jakunzler/bancada-didatica/imagens/800px-Microrregiao_do_Moxoto.png

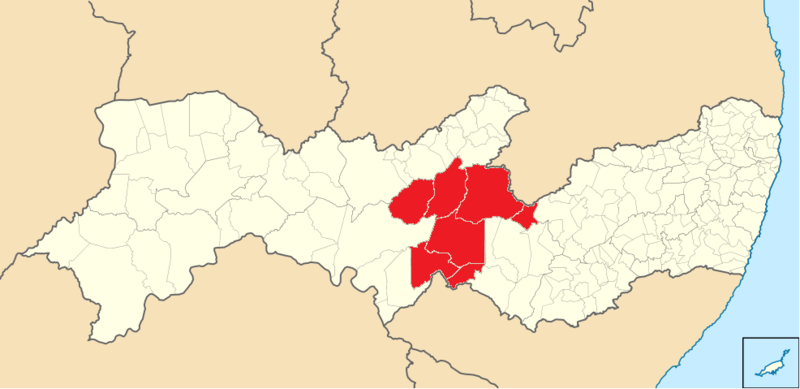
imagens/800px-Microrregiao_do_Moxoto.png
