jakunzler/bancada-didatica/imagens/BancadaDidaticaAutomacaoTras.jpeg

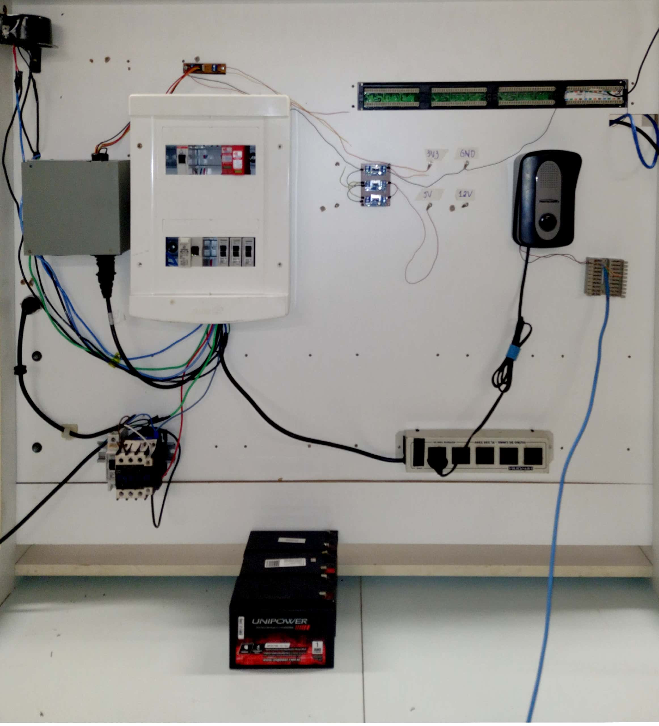
imagens/BancadaDidaticaAutomacaoTras.jpeg
