jakunzler/bancada-didatica/imagens/lampada_espia.webp

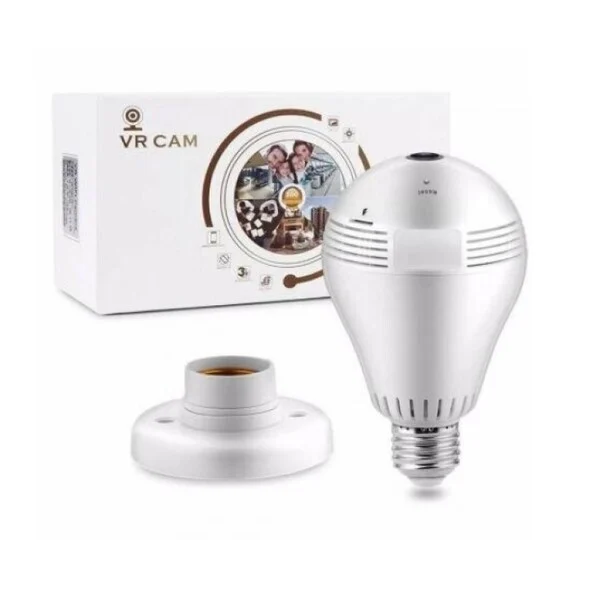
imagens/lampada_espia.webp
