jakunzler/bancada-didatica/imagens/rfid.webp

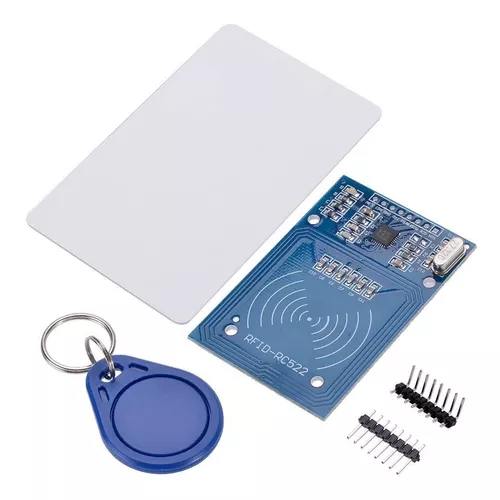
imagens/rfid.webp
