jakunzler/bancada-didatica/imagens/rfid_pin.webp

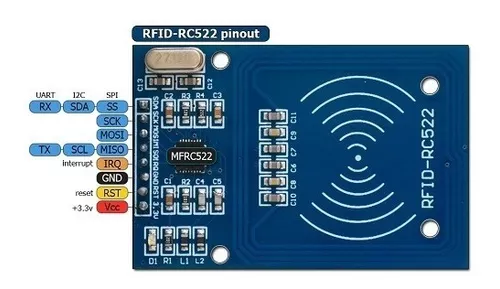
imagens/rfid_pin.webp
