jakunzler/bancada-didatica/imagens/rfid_pin_arduino.webp

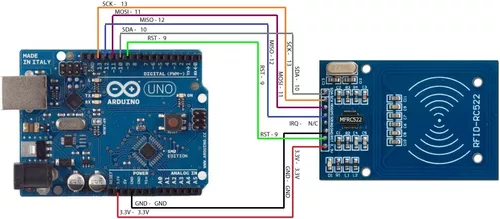
imagens/rfid_pin_arduino.webp
